cryptovillage/badge2017/assets/images/bender.png

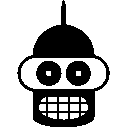
assets/images/bender.png
