cryptovillage/badge2017/assets/images/clubmate.png

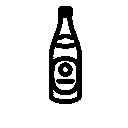
assets/images/clubmate.png
