cryptovillage/badge2017/assets/images/rot.png

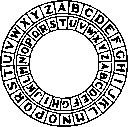
assets/images/rot.png
