cryptovillage/badge2017/assets/images/unlock.png

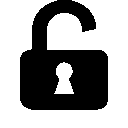
assets/images/unlock.png
