cryptovillage/badge2017/firmware/efm8ub1/src/InitDevice.c

//=========================================================
// src/InitDevice.c: generated by Hardware Configurator
//
// This file will be regenerated when saving a document.
// leave the sections inside the "$[...]" comment tags alone
// or they will be overwritten!
//=========================================================

// USER INCLUDES
#include <SI_EFM8UB1_Register_Enums.h>
#include "InitDevice.h"
#include "board.h"

// USER PROTOTYPES
// USER FUNCTIONS

// $[Library Includes]
#include "efm8_usb.h"
#include "descriptors.h"
#include "usb_0.h"
// [Library Includes]$

//==============================================================================
// enter_DefaultMode_from_RESET
//==============================================================================
extern void enter_DefaultMode_from_RESET(void) {
	// $[Config Calls]
	// Save the SFRPAGE
	uint8_t SFRPAGE_save = SFRPAGE;
	WDT_0_enter_DefaultMode_from_RESET();
	VREG_0_enter_DefaultMode_from_RESET();
	PORTS_0_enter_DefaultMode_from_RESET();
	PORTS_1_enter_DefaultMode_from_RESET();
	PORTS_2_enter_DefaultMode_from_RESET();
	PBCFG_0_enter_DefaultMode_from_RESET();
	ADC_0_enter_DefaultMode_from_RESET();
	CMP_0_enter_DefaultMode_from_RESET();
	CIP51_0_enter_DefaultMode_from_RESET();
	CLOCK_0_enter_DefaultMode_from_RESET();
	TIMER01_0_enter_DefaultMode_from_RESET();
	TIMER16_2_enter_DefaultMode_from_RESET();
	TIMER_SETUP_0_enter_DefaultMode_from_RESET();
	PCA_0_enter_DefaultMode_from_RESET();
	PCACH_0_enter_DefaultMode_from_RESET();
	SMBUS_0_enter_DefaultMode_from_RESET();
	SPI_0_enter_DefaultMode_from_RESET();
	UART_0_enter_DefaultMode_from_RESET();
	INTERRUPT_0_enter_DefaultMode_from_RESET();
	USBLIB_0_enter_DefaultMode_from_RESET();
	// Restore the SFRPAGE
	SFRPAGE = SFRPAGE_save;
	// [Config Calls]$
}

extern void VREG_0_enter_DefaultMode_from_RESET(void) {
	// $[REG0CN - Voltage Regulator 0 Control]
	// [REG0CN - Voltage Regulator 0 Control]$

	// $[REG1CN - Voltage Regulator 1 Control]
	/***********************************************************************
	 - Regulator is disabled
	 - Regulator bias is enabled
	 - The 5V regulator is in normal power mode
	 ***********************************************************************/
	SFRPAGE = 0x20;
	REG1CN = REG1CN_REG1ENB__DISABLED | REG1CN_BIASENB__ENABLED
			| REG1CN_SUSEN__NORMAL;
	// [REG1CN - Voltage Regulator 1 Control]$

}

extern void CIP51_0_enter_DefaultMode_from_RESET(void) {

	// $[PFE0CN - Prefetch Engine Control]
	/***********************************************************************
	 - Enable the prefetch engine 
	 - SYSCLK < 50 MHz
	 ***********************************************************************/
	SFRPAGE = 0x10;
	PFE0CN = PFE0CN_PFEN__ENABLED | PFE0CN_FLRT__SYSCLK_BELOW_50_MHZ;
	// [PFE0CN - Prefetch Engine Control]$

}

extern void PORTS_0_enter_DefaultMode_from_RESET(void) {
	// $[P0 - Port 0 Pin Latch]
	// [P0 - Port 0 Pin Latch]$

	// $[P0MDOUT - Port 0 Output Mode]
	/***********************************************************************
	 - P0.0 output is open-drain
	 - P0.1 output is open-drain
	 - P0.2 output is open-drain
	 - P0.3 output is open-drain
	 - P0.4 output is push-pull
	 - P0.5 output is open-drain
	 - P0.6 output is open-drain
	 - P0.7 output is open-drain
	 ***********************************************************************/
	SFRPAGE = 0x00;
	P0MDOUT = P0MDOUT_B0__OPEN_DRAIN | P0MDOUT_B1__OPEN_DRAIN
			| P0MDOUT_B2__OPEN_DRAIN | P0MDOUT_B3__OPEN_DRAIN
			| P0MDOUT_B4__PUSH_PULL | P0MDOUT_B5__OPEN_DRAIN
			| P0MDOUT_B6__OPEN_DRAIN | P0MDOUT_B7__OPEN_DRAIN;
	// [P0MDOUT - Port 0 Output Mode]$

	// $[P0MDIN - Port 0 Input Mode]
	/***********************************************************************
	 - P0.0 pin is configured for digital mode
	 - P0.1 pin is configured for digital mode
	 - P0.2 pin is configured for digital mode
	 - P0.3 pin is configured for digital mode
	 - P0.4 pin is configured for digital mode
	 - P0.5 pin is configured for digital mode
	 - P0.6 pin is configured for analog mode
	 - P0.7 pin is configured for analog mode
	 ***********************************************************************/
	P0MDIN = P0MDIN_B0__DIGITAL | P0MDIN_B1__DIGITAL | P0MDIN_B2__DIGITAL
			| P0MDIN_B3__DIGITAL | P0MDIN_B4__DIGITAL | P0MDIN_B5__DIGITAL
			| P0MDIN_B6__ANALOG | P0MDIN_B7__ANALOG;
	// [P0MDIN - Port 0 Input Mode]$

	// $[P0SKIP - Port 0 Skip]
	/***********************************************************************
	 - P0.0 pin is skipped by the crossbar
	 - P0.1 pin is skipped by the crossbar
	 - P0.2 pin is skipped by the crossbar
	 - P0.3 pin is skipped by the crossbar
	 - P0.4 pin is not skipped by the crossbar
	 - P0.5 pin is not skipped by the crossbar
	 - P0.6 pin is skipped by the crossbar
	 - P0.7 pin is skipped by the crossbar
	 ***********************************************************************/
	P0SKIP = P0SKIP_B0__SKIPPED | P0SKIP_B1__SKIPPED | P0SKIP_B2__SKIPPED
			| P0SKIP_B3__SKIPPED | P0SKIP_B4__NOT_SKIPPED
			| P0SKIP_B5__NOT_SKIPPED | P0SKIP_B6__SKIPPED | P0SKIP_B7__SKIPPED;
	// [P0SKIP - Port 0 Skip]$

	// $[P0MASK - Port 0 Mask]
	// [P0MASK - Port 0 Mask]$

	// $[P0MAT - Port 0 Match]
	// [P0MAT - Port 0 Match]$

	P0 = 0x0e;
}

extern void PBCFG_0_enter_DefaultMode_from_RESET(void) {
	// $[XBR2 - Port I/O Crossbar 2]
	/***********************************************************************
	 - Weak Pullups enabled 
	 - Crossbar enabled
	 - UART1 I/O unavailable at Port pin
	 - UART1 RTS1 unavailable at Port pin
	 - UART1 CTS1 unavailable at Port pin
	 ***********************************************************************/
	SFRPAGE = 0x00;
	XBR2 = XBR2_WEAKPUD__PULL_UPS_ENABLED | XBR2_XBARE__ENABLED
			| XBR2_URT1E__DISABLED | XBR2_URT1RTSE__DISABLED
			| XBR2_URT1CTSE__DISABLED;
	// [XBR2 - Port I/O Crossbar 2]$

	// $[PRTDRV - Port Drive Strength]
	// [PRTDRV - Port Drive Strength]$

	// $[XBR0 - Port I/O Crossbar 0]
	/***********************************************************************
	 - UART0 TX0, RX0 routed to Port pins P0.4 and P0.5
	 - SPI I/O routed to Port pins
	 - SMBus 0 I/O routed to Port pins
	 - CP0 unavailable at Port pin
	 - Asynchronous CP0 unavailable at Port pin
	 - CP1 unavailable at Port pin
	 - Asynchronous CP1 unavailable at Port pin
	 - SYSCLK unavailable at Port pin
	 ***********************************************************************/
	XBR0 = XBR0_URT0E__ENABLED | XBR0_SPI0E__ENABLED | XBR0_SMB0E__ENABLED
			| XBR0_CP0E__DISABLED | XBR0_CP0AE__DISABLED | XBR0_CP1E__DISABLED
			| XBR0_CP1AE__DISABLED | XBR0_SYSCKE__DISABLED;
	// [XBR0 - Port I/O Crossbar 0]$

	// $[XBR1 - Port I/O Crossbar 1]
	/***********************************************************************
	 - CEX0 routed to Port pin
	 - ECI unavailable at Port pin
	 - T0 unavailable at Port pin
	 - T1 unavailable at Port pin
	 - T2 unavailable at Port pin
	 ***********************************************************************/
	XBR1 = XBR1_PCA0ME__CEX0 | XBR1_ECIE__DISABLED | XBR1_T0E__DISABLED
			| XBR1_T1E__DISABLED | XBR1_T2E__DISABLED;
	// [XBR1 - Port I/O Crossbar 1]$

}

extern void CLOCK_0_enter_DefaultMode_from_RESET(void) {
	// $[HFOSC1 Setup]
	// Ensure SYSCLK is > 24 MHz before switching to HFOSC1
	SFRPAGE = 0x00;
	CLKSEL = CLKSEL_CLKSL__HFOSC0 | CLKSEL_CLKDIV__SYSCLK_DIV_1;
	while ((CLKSEL & CLKSEL_DIVRDY__BMASK) == CLKSEL_DIVRDY__NOT_READY)
		;
	// [HFOSC1 Setup]$

	// $[CLKSEL - Clock Select]
	/***********************************************************************
	 - Clock derived from the Internal High Frequency Oscillator 1
	 - SYSCLK is equal to selected clock source divided by 1
	 ***********************************************************************/
	CLKSEL = CLKSEL_CLKSL__HFOSC1 | CLKSEL_CLKDIV__SYSCLK_DIV_1;
	while ((CLKSEL & CLKSEL_DIVRDY__BMASK) == CLKSEL_DIVRDY__NOT_READY)
		;
	// [CLKSEL - Clock Select]$

}

extern void INTERRUPT_0_enter_DefaultMode_from_RESET(void) {
	// $[EIE1 - Extended Interrupt Enable 1]
	/***********************************************************************
	 - Enable interrupt requests generated by the ADINT flag
	 - Disable ADC0 Window Comparison interrupt
	 - Enable interrupt requests generated by the comparator 0 CPRIF or CPFIF
	 flags
	 - Disable CP1 interrupts
	 - Disable all Port Match interrupts
	 - Disable all PCA0 interrupts
	 - Enable interrupt requests generated by SMB0
	 - Disable Timer 3 interrupts
	 ***********************************************************************/
	EIE1 = EIE1_EADC0__ENABLED | EIE1_EWADC0__DISABLED | EIE1_ECP0__ENABLED
			| EIE1_ECP1__DISABLED | EIE1_EMAT__DISABLED | EIE1_EPCA0__DISABLED
			| EIE1_ESMB0__ENABLED | EIE1_ET3__DISABLED;
	// [EIE1 - Extended Interrupt Enable 1]$

	// $[EIE2 - Extended Interrupt Enable 2]
	/***********************************************************************
	 - Disable all I2C0 slave interrupts
	 - Disable Timer 4 interrupts
	 - Disable UART1 interrupts
	 - Disable all USB0 interrupts
	 - Enable interrupt requests generated by VBUS and VBUS and USB Charger
	 Detect
	 ***********************************************************************/
	SFRPAGE = 0x10;
	EIE2 = EIE2_EI2C0__DISABLED | EIE2_ET4__DISABLED | EIE2_ES1__DISABLED
			| EIE2_EUSB0__DISABLED | EIE2_EVBUS__ENABLED;
	// [EIE2 - Extended Interrupt Enable 2]$

	// $[EIP1H - Extended Interrupt Priority 1 High]
	// [EIP1H - Extended Interrupt Priority 1 High]$

	// $[EIP1 - Extended Interrupt Priority 1 Low]
	// [EIP1 - Extended Interrupt Priority 1 Low]$

	// $[EIP2 - Extended Interrupt Priority 2]
	// [EIP2 - Extended Interrupt Priority 2]$

	// $[EIP2H - Extended Interrupt Priority 2 High]
	// [EIP2H - Extended Interrupt Priority 2 High]$

	// $[IE - Interrupt Enable]
	/***********************************************************************
	 - Enable each interrupt according to its individual mask setting
	 - Disable external interrupt 0
	 - Disable external interrupt 1
	 - Enable interrupt requests generated by SPI0
	 - Disable all Timer 0 interrupt
	 - Disable all Timer 1 interrupt
	 - Enable interrupt requests generated by the TF2L or TF2H flags
	 - Enable UART0 interrupt
	 ***********************************************************************/
	SFRPAGE = 0x00;
	IE = IE_EA__ENABLED | IE_EX0__DISABLED | IE_EX1__DISABLED
			| IE_ESPI0__ENABLED | IE_ET0__DISABLED | IE_ET1__DISABLED
			| IE_ET2__ENABLED | IE_ES0__ENABLED;
	// [IE - Interrupt Enable]$

	// $[IP - Interrupt Priority]
	// [IP - Interrupt Priority]$

	// $[IPH - Interrupt Priority High]
	// [IPH - Interrupt Priority High]$

}

static const uint8_t code uuid[16] _at_ 0xFFC0;

extern void USBLIB_0_enter_DefaultMode_from_RESET(void) {
	// Read in UUID
	SI_SEGMENT_VARIABLE(hex[], static const uint8_t, SI_SEG_CODE) =
	{	'0', '1', '2', '3', '4', '5', '6', '7',
		'8', '9', 'a', 'b', 'c', 'd', 'e', 'f'};
	uint8_t i;

	for (i = 0; i < 16; i++) {
		serDesc[i * 2 + 3] = hex[(uuid[i] >> 4)];
		serDesc[i * 2 + 4] = hex[uuid[i] & 0xf];
	}

	// $[USBD Init]
	USBD_Init (&initstruct);
	// [USBD Init]$

}

extern void PORTS_1_enter_DefaultMode_from_RESET(void) {
	// $[P1 - Port 1 Pin Latch]
	// [P1 - Port 1 Pin Latch]$

	// $[P1MDOUT - Port 1 Output Mode]
	/***********************************************************************
	 - P1.0 output is push-pull
	 - P1.1 output is open-drain
	 - P1.2 output is push-pull
	 - P1.3 output is push-pull
	 - P1.4 output is open-drain
	 - P1.5 output is open-drain
	 - P1.6 output is open-drain
	 - P1.7 output is push-pull
	 ***********************************************************************/
	P1MDOUT = P1MDOUT_B0__PUSH_PULL | P1MDOUT_B1__OPEN_DRAIN
			| P1MDOUT_B2__PUSH_PULL | P1MDOUT_B3__PUSH_PULL
			| P1MDOUT_B4__OPEN_DRAIN | P1MDOUT_B5__OPEN_DRAIN
			| P1MDOUT_B6__OPEN_DRAIN | P1MDOUT_B7__PUSH_PULL;
	// [P1MDOUT - Port 1 Output Mode]$

	// $[P1MDIN - Port 1 Input Mode]
	// [P1MDIN - Port 1 Input Mode]$

	// $[P1SKIP - Port 1 Skip]
	/***********************************************************************
	 - P1.0 pin is not skipped by the crossbar
	 - P1.1 pin is not skipped by the crossbar
	 - P1.2 pin is not skipped by the crossbar
	 - P1.3 pin is skipped by the crossbar
	 - P1.4 pin is skipped by the crossbar
	 - P1.5 pin is not skipped by the crossbar
	 - P1.6 pin is not skipped by the crossbar
	 - P1.7 pin is skipped by the crossbar
	 ***********************************************************************/
	P1SKIP = P1SKIP_B0__NOT_SKIPPED | P1SKIP_B1__NOT_SKIPPED
			| P1SKIP_B2__NOT_SKIPPED | P1SKIP_B3__SKIPPED | P1SKIP_B4__SKIPPED
			| P1SKIP_B5__NOT_SKIPPED | P1SKIP_B6__NOT_SKIPPED
			| P1SKIP_B7__SKIPPED;
	// [P1SKIP - Port 1 Skip]$

	// $[P1MASK - Port 1 Mask]
	// [P1MASK - Port 1 Mask]$

	// $[P1MAT - Port 1 Match]
	// [P1MAT - Port 1 Match]$

	ESP32_EN = 0; // Disable ESP32 for now
	ESP32_BOOT = ESP32_BOOT_IDLE; // Don't enable BOOT pulldown
}

extern void SPI_0_enter_DefaultMode_from_RESET(void) {
	// $[SPI0CKR - SPI0 Clock Rate]
	/***********************************************************************
	 - SPI0 Clock Rate = 0x01
	 ***********************************************************************/
	SPI0CKR = (0x01 << SPI0CKR_SPI0CKR__SHIFT);
	// [SPI0CKR - SPI0 Clock Rate]$

	// $[SPI0FCN0 - SPI0 FIFO Control 0]
	/***********************************************************************
	 - RFRQ will be set anytime new data arrives in the RX FIFO 
	 - TFRQ will be set when the TX FIFO contains three or fewer bytes
	 - SPI0 interrupts will not be generated when RFRQ is set
	 - SPI0 interrupts will not be generated when TFRQ is set
	 ***********************************************************************/
	SFRPAGE = 0x20;
	SPI0FCN0 = SPI0FCN0_RXTH__ZERO | SPI0FCN0_TXTH__THREE
			| SPI0FCN0_RFRQE__DISABLED | SPI0FCN0_TFRQE__DISABLED;
	// [SPI0FCN0 - SPI0 FIFO Control 0]$

	// $[SPI0FCN1 - SPI0 FIFO Control 1]
	/***********************************************************************
	 - Received bytes will be discarded
	 - SPI0 interrupts will not be generated when SPIF is set
	 ***********************************************************************/
	SPI0FCN1 &= ~(SPI0FCN1_RXFIFOE__BMASK | SPI0FCN1_SPIFEN__BMASK);
	// [SPI0FCN1 - SPI0 FIFO Control 1]$

	// $[SPI0CFG - SPI0 Configuration]
	/***********************************************************************
	 - Enable master mode. Operate as a master
	 ***********************************************************************/
	SFRPAGE = 0x00;
	SPI0CFG |= SPI0CFG_MSTEN__MASTER_ENABLED;
	// [SPI0CFG - SPI0 Configuration]$

	// $[SPI0CN0 - SPI0 Control]
	/***********************************************************************
	 - Enable the SPI module
	 - 3-Wire Slave or 3-Wire Master Mode
	 ***********************************************************************/
	SPI0CN0 &= ~SPI0CN0_NSSMD__FMASK;
	SPI0CN0 |= SPI0CN0_SPIEN__ENABLED;
	// [SPI0CN0 - SPI0 Control]$

}

extern void PORTS_2_enter_DefaultMode_from_RESET(void) {
	// $[P2 - Port 2 Pin Latch]
	// [P2 - Port 2 Pin Latch]$

	// $[P2MDOUT - Port 2 Output Mode]
	/***********************************************************************
	 - P2.0 output is push-pull
	 - P2.1 output is push-pull
	 - P2.2 output is push-pull
	 - P2.3 output is push-pull
	 ***********************************************************************/
	P2MDOUT = P2MDOUT_B0__PUSH_PULL | P2MDOUT_B1__PUSH_PULL
			| P2MDOUT_B2__PUSH_PULL | P2MDOUT_B3__PUSH_PULL;
	// [P2MDOUT - Port 2 Output Mode]$

	// $[P2MDIN - Port 2 Input Mode]
	// [P2MDIN - Port 2 Input Mode]$

	// $[P2SKIP - Port 2 Skip]
	/***********************************************************************
	 - P2.0 pin is skipped by the crossbar
	 - P2.1 pin is not skipped by the crossbar
	 - P2.2 pin is not skipped by the crossbar
	 - P2.3 pin is not skipped by the crossbar
	 ***********************************************************************/
	SFRPAGE = 0x20;
	P2SKIP = P2SKIP_B0__SKIPPED | P2SKIP_B1__NOT_SKIPPED
			| P2SKIP_B2__NOT_SKIPPED | P2SKIP_B3__NOT_SKIPPED;
	// [P2SKIP - Port 2 Skip]$

	// $[P2MASK - Port 2 Mask]
	// [P2MASK - Port 2 Mask]$

	// $[P2MAT - Port 2 Match]
	// [P2MAT - Port 2 Match]$

	MIC_SHDN = 1; // Shut down MIC amp for now
	BC_EN_1 = 0; // Disable charging
	BC_EN_2 = 0; // Disable charging
}

extern void ADC_0_enter_DefaultMode_from_RESET(void) {
	// $[ADC0CN1 - ADC0 Control 1]
	// [ADC0CN1 - ADC0 Control 1]$

	// $[ADC0MX - ADC0 Multiplexer Selection]
	/***********************************************************************
	 - Select ADC0.7
	 ***********************************************************************/
	ADC0MX = ADC0MX_ADC0MX__ADC0P7;
	// [ADC0MX - ADC0 Multiplexer Selection]$

	// $[ADC0CF - ADC0 Configuration]
	/***********************************************************************
	 - SAR Clock Divider = 0x06
	 - ADC0 operates in 10-bit or 12-bit mode 
	 - The on-chip PGA gain is 1
	 - Normal Track Mode
	 ***********************************************************************/
	ADC0CF = (0x06 << ADC0CF_ADSC__SHIFT) | ADC0CF_AD8BE__NORMAL
			| ADC0CF_ADGN__GAIN_1 | ADC0CF_ADTM__TRACK_NORMAL;
	// [ADC0CF - ADC0 Configuration]$

	// $[ADC0AC - ADC0 Accumulator Configuration]
	// [ADC0AC - ADC0 Accumulator Configuration]$

	// $[ADC0TK - ADC0 Burst Mode Track Time]
	// [ADC0TK - ADC0 Burst Mode Track Time]$

	// $[ADC0PWR - ADC0 Power Control]
	/***********************************************************************
	 - Burst Mode Power Up Time = 0x0F
	 - Enable low power mode 
	 - Low power mode disabled
	 - Select bias current mode 1 
	 ***********************************************************************/
	ADC0PWR = (0x0F << ADC0PWR_ADPWR__SHIFT) | ADC0PWR_ADLPM__LP_BUFFER_ENABLED
			| ADC0PWR_ADMXLP__LP_MUX_VREF_DISABLED | ADC0PWR_ADBIAS__MODE1;
	// [ADC0PWR - ADC0 Power Control]$

	// $[ADC0GTH - ADC0 Greater-Than High Byte]
	// [ADC0GTH - ADC0 Greater-Than High Byte]$

	// $[ADC0GTL - ADC0 Greater-Than Low Byte]
	// [ADC0GTL - ADC0 Greater-Than Low Byte]$

	// $[ADC0LTH - ADC0 Less-Than High Byte]
	// [ADC0LTH - ADC0 Less-Than High Byte]$

	// $[ADC0LTL - ADC0 Less-Than Low Byte]
	// [ADC0LTL - ADC0 Less-Than Low Byte]$

	// $[ADC0CN0 - ADC0 Control 0]
	/***********************************************************************
	 - Enable ADC0 burst mode
	 ***********************************************************************/
	ADC0CN0 |= ADC0CN0_ADBMEN__BURST_ENABLED;
	// [ADC0CN0 - ADC0 Control 0]$

}

extern void TIMER_SETUP_0_enter_DefaultMode_from_RESET(void) {
	// $[CKCON0 - Clock Control 0]
	/***********************************************************************
	 - System clock divided by 12
	 - Counter/Timer 0 uses the system clock
	 - Timer 2 high byte uses the clock defined by T2XCLK in TMR2CN0
	 - Timer 2 low byte uses the clock defined by T2XCLK in TMR2CN0
	 - Timer 3 high byte uses the clock defined by T3XCLK in TMR3CN0
	 - Timer 3 low byte uses the clock defined by T3XCLK in TMR3CN0
	 - Timer 1 uses the system clock
	 ***********************************************************************/
	CKCON0 = CKCON0_SCA__SYSCLK_DIV_12 | CKCON0_T0M__SYSCLK
			| CKCON0_T2MH__EXTERNAL_CLOCK | CKCON0_T2ML__EXTERNAL_CLOCK
			| CKCON0_T3MH__EXTERNAL_CLOCK | CKCON0_T3ML__EXTERNAL_CLOCK
			| CKCON0_T1M__SYSCLK;
	// [CKCON0 - Clock Control 0]$

	// $[CKCON1 - Clock Control 1]
	// [CKCON1 - Clock Control 1]$

	// $[TMOD - Timer 0/1 Mode]
	/***********************************************************************
	 - Mode 2, 8-bit Counter/Timer with Auto-Reload
	 - Mode 2, 8-bit Counter/Timer with Auto-Reload
	 - Timer Mode
	 - Timer 0 enabled when TR0 = 1 irrespective of INT0 logic level
	 - Timer Mode
	 - Timer 1 enabled when TR1 = 1 irrespective of INT1 logic level
	 ***********************************************************************/
	TMOD = TMOD_T0M__MODE2 | TMOD_T1M__MODE2 | TMOD_CT0__TIMER
			| TMOD_GATE0__DISABLED | TMOD_CT1__TIMER | TMOD_GATE1__DISABLED;
	// [TMOD - Timer 0/1 Mode]$

	// $[TCON - Timer 0/1 Control]
	/***********************************************************************
	 - Start Timer 0 running
	 - Start Timer 1 running
	 ***********************************************************************/
	TCON |= TCON_TR0__RUN | TCON_TR1__RUN;
	// [TCON - Timer 0/1 Control]$

}

extern void UART_0_enter_DefaultMode_from_RESET(void) {
	// $[SCON0 - UART0 Serial Port Control]
	/***********************************************************************
	 - UART0 reception enabled
	 ***********************************************************************/
	SCON0 |= SCON0_REN__RECEIVE_ENABLED;
	// [SCON0 - UART0 Serial Port Control]$

}

extern void SMBUS_0_enter_DefaultMode_from_RESET(void) {
	// $[SMB0FCN0 - SMBus0 FIFO Control 0]
	// [SMB0FCN0 - SMBus0 FIFO Control 0]$

	// $[SMB0RXLN - SMBus0 Receive Length Counter]
	// [SMB0RXLN - SMBus0 Receive Length Counter]$

	// $[SMB0ADR - SMBus 0 Slave Address]
	/***********************************************************************
	 - General Call Address is ignored
	 - SMBus Hardware Slave Address = 0x64
	 ***********************************************************************/
	SMB0ADR = SMB0ADR_GC__IGNORED | (0x64 << SMB0ADR_SLV__SHIFT);
	// [SMB0ADR - SMBus 0 Slave Address]$

	// $[SMB0ADM - SMBus 0 Slave Address Mask]
	/***********************************************************************
	 - Automatic slave address recognition and hardware acknowledge is
	 enabled
	 - SMBus Slave Address Mask = 0x7F
	 ***********************************************************************/
	SMB0ADM = SMB0ADM_EHACK__ADR_ACK_AUTOMATIC | (0x7F << SMB0ADM_SLVM__SHIFT);
	// [SMB0ADM - SMBus 0 Slave Address Mask]$

	// $[SMB0TC - SMBus 0 Timing and Pin Control]
	// [SMB0TC - SMBus 0 Timing and Pin Control]$

	// $[SMB0CF - SMBus 0 Configuration]
	/***********************************************************************
	 - Slave states are inhibited
	 - Enable the SMBus module
	 ***********************************************************************/
	SMB0CF |= SMB0CF_INH__SLAVE_DISABLED | SMB0CF_ENSMB__ENABLED;
	// [SMB0CF - SMBus 0 Configuration]$

}

extern void TIMER01_0_enter_DefaultMode_from_RESET(void) {
	// $[Timer Initialization]
	//Save Timer Configuration
	uint8_t TCON_save;
	TCON_save = TCON;
	//Stop Timers
	TCON &= ~TCON_TR0__BMASK & ~TCON_TR1__BMASK;

	// [Timer Initialization]$

	// $[TH0 - Timer 0 High Byte]
	/***********************************************************************
	 - Timer 0 High Byte = 0xD8
	 ***********************************************************************/
	TH0 = (0xD8 << TH0_TH0__SHIFT);
	// [TH0 - Timer 0 High Byte]$

	// $[TL0 - Timer 0 Low Byte]
	// [TL0 - Timer 0 Low Byte]$

	// $[TH1 - Timer 1 High Byte]
	/***********************************************************************
	 - Timer 1 High Byte = 0x30
	 ***********************************************************************/
	TH1 = (0x30 << TH1_TH1__SHIFT);
	// [TH1 - Timer 1 High Byte]$

	// $[TL1 - Timer 1 Low Byte]
	// [TL1 - Timer 1 Low Byte]$

	// $[Timer Restoration]
	//Restore Timer Configuration
	TCON |= (TCON_save & TCON_TR0__BMASK) | (TCON_save & TCON_TR1__BMASK);

	// [Timer Restoration]$

}

extern void WDT_0_enter_DefaultMode_from_RESET(void) {
	// $[WDTCN - Watchdog Timer Control]
	SFRPAGE = 0x00;
	//Disable Watchdog with key sequence
	WDTCN = 0xDE; //First key
	WDTCN = 0xAD; //Second key
	// [WDTCN - Watchdog Timer Control]$
	// WDTCN = 0xff; // Prevent watchdog from being disabled
}

extern void CMP_0_enter_DefaultMode_from_RESET(void) {
	// $[CMP0MX - Comparator 0 Multiplexer Selection]
	/***********************************************************************
	 - External pin CMP0P.8
	 - External pin CMP0N.6
	 ***********************************************************************/
	uint8_t delay;

	CMP0MX = CMP0MX_CMXP__CMP0P8 | CMP0MX_CMXN__CMP0N6;
	// Delay to allow the comparator inputs to settle
	for (delay = 0; delay < 0x20; delay++)
		;
	// [CMP0MX - Comparator 0 Multiplexer Selection]$

	// $[CMP0CN1 - Comparator 0 Control 1]
	// [CMP0CN1 - Comparator 0 Control 1]$

	// $[CMP0MD - Comparator 0 Mode]
	/***********************************************************************
	 - Mode 3 
	 - Output is inverted
	 - Comparator falling-edge interrupt enabled
	 - Comparator rising-edge interrupt enabled
	 ***********************************************************************/
	CMP0MD |= CMP0MD_CPMD__MODE3 | CMP0MD_CPINV__INVERT
			| CMP0MD_CPFIE__FALL_INT_ENABLED | CMP0MD_CPRIE__RISE_INT_ENABLED;
	// [CMP0MD - Comparator 0 Mode]$

	// $[CMP0CN0 - Comparator 0 Control 0]
	/***********************************************************************
	 - Comparator enabled
	 - Positive Hysteresis = Hysteresis 3 
	 - Negative Hysteresis = Hysteresis 3 
	 ***********************************************************************/
	CMP0CN0 |= CMP0CN0_CPEN__ENABLED | CMP0CN0_CPHYP__ENABLED_MODE3
			| CMP0CN0_CPHYN__ENABLED_MODE3;
	// [CMP0CN0 - Comparator 0 Control 0]$

}

extern void PCA_0_enter_DefaultMode_from_RESET(void) {
	// $[PCA Off]
	PCA0CN0_CR = PCA0CN0_CR__STOP;
	// [PCA Off]$

	// $[PCA0MD - PCA Mode]
	// [PCA0MD - PCA Mode]$

	// $[PCA0CENT - PCA Center Alignment Enable]
	// [PCA0CENT - PCA Center Alignment Enable]$

	// $[PCA0CLR - PCA Comparator Clear Control]
	// [PCA0CLR - PCA Comparator Clear Control]$

	// $[PCA0L - PCA Counter/Timer Low Byte]
	// [PCA0L - PCA Counter/Timer Low Byte]$

	// $[PCA0H - PCA Counter/Timer High Byte]
	// [PCA0H - PCA Counter/Timer High Byte]$

	// $[PCA0POL - PCA Output Polarity]
	/***********************************************************************
	 - Invert polarity
	 - Use default polarity
	 - Use default polarity
	 ***********************************************************************/
	PCA0POL = PCA0POL_CEX0POL__INVERT | PCA0POL_CEX1POL__DEFAULT
			| PCA0POL_CEX2POL__DEFAULT;
	// [PCA0POL - PCA Output Polarity]$

	// $[PCA0PWM - PCA PWM Configuration]
	// [PCA0PWM - PCA PWM Configuration]$

	// $[PCA On]
	PCA0CN0_CR = PCA0CN0_CR__RUN;
	// [PCA On]$

}

extern void PCACH_0_enter_DefaultMode_from_RESET(void) {
	// $[PCA0 Settings Save]
	// Select Capture/Compare register)
	PCA0PWM &= ~PCA0PWM_ARSEL__BMASK;
	// [PCA0 Settings Save]$

	// $[PCA0CPM0 - PCA Channel 0 Capture/Compare Mode]
	/***********************************************************************
	 - Disable negative edge capture
	 - Disable CCF0 interrupts
	 - Disable match function
	 - 8 to 11-bit PWM selected
	 - Disable positive edge capture
	 - Enable comparator function
	 - Enable PWM function
	 - Disable toggle function
	 ***********************************************************************/
	PCA0CPM0 = PCA0CPM0_CAPN__DISABLED | PCA0CPM0_ECCF__DISABLED
			| PCA0CPM0_MAT__DISABLED | PCA0CPM0_PWM16__8_BIT
			| PCA0CPM0_CAPP__DISABLED | PCA0CPM0_ECOM__ENABLED
			| PCA0CPM0_PWM__ENABLED | PCA0CPM0_TOG__DISABLED;
	// [PCA0CPM0 - PCA Channel 0 Capture/Compare Mode]$

	// $[PCA0CPL0 - PCA Channel 0 Capture Module Low Byte]
	// [PCA0CPL0 - PCA Channel 0 Capture Module Low Byte]$

	// $[PCA0CPH0 - PCA Channel 0 Capture Module High Byte]
	// [PCA0CPH0 - PCA Channel 0 Capture Module High Byte]$

	// $[Auto-reload]
	// [Auto-reload]$

	// $[PCA0 Settings Restore]
	// [PCA0 Settings Restore]$

}

extern void TIMER16_2_enter_DefaultMode_from_RESET(void) {
	// $[Timer Initialization]
	// Save Timer Configuration
	uint8_t TMR2CN0_TR2_save;
	TMR2CN0_TR2_save = TMR2CN0 & TMR2CN0_TR2__BMASK;
	// Stop Timer
	TMR2CN0 &= ~(TMR2CN0_TR2__BMASK);
	// [Timer Initialization]$

	// $[TMR2CN1 - Timer 2 Control 1]
	// [TMR2CN1 - Timer 2 Control 1]$

	// $[TMR2CN0 - Timer 2 Control]
	// [TMR2CN0 - Timer 2 Control]$

	// $[TMR2H - Timer 2 High Byte]
	// [TMR2H - Timer 2 High Byte]$

	// $[TMR2L - Timer 2 Low Byte]
	// [TMR2L - Timer 2 Low Byte]$

	// $[TMR2RLH - Timer 2 Reload High Byte]
	/***********************************************************************
	 - Timer 2 Reload High Byte = 0xFE
	 ***********************************************************************/
	TMR2RLH = (0xFE << TMR2RLH_TMR2RLH__SHIFT);
	// [TMR2RLH - Timer 2 Reload High Byte]$

	// $[TMR2RLL - Timer 2 Reload Low Byte]
	/***********************************************************************
	 - Timer 2 Reload Low Byte = 0x70
	 ***********************************************************************/
	TMR2RLL = (0x70 << TMR2RLL_TMR2RLL__SHIFT);
	// [TMR2RLL - Timer 2 Reload Low Byte]$

	// $[TMR2CN0]
	/***********************************************************************
	 - Start Timer 2 running
	 ***********************************************************************/
	TMR2CN0 |= TMR2CN0_TR2__RUN;
	// [TMR2CN0]$

	// $[Timer Restoration]
	// Restore Timer Configuration
	TMR2CN0 |= TMR2CN0_TR2_save;
	// [Timer Restoration]$

}
