cryptovillage/badge2017/firmware/esp32/components/micropython/src/modmachine.c

/*
 * This file is part of the MicroPython project, http://micropython.org/
 *
 * Development of the code in this file was sponsored by Microbric Pty Ltd
 *
 * The MIT License (MIT)
 *
 * Copyright (c) 2013-2015 Damien P. George
 * Copyright (c) 2016 Paul Sokolovsky
 *
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
 * THE SOFTWARE IS PROVIDED "AS IS", WITHOUT WARRANTY OF ANY KIND, EXPRESS OR
 * IMPLIED, INCLUDING BUT NOT LIMITED TO THE WARRANTIES OF MERCHANTABILITY,
 * FITNESS FOR A PARTICULAR PURPOSE AND NONINFRINGEMENT. IN NO EVENT SHALL THE
 * AUTHORS OR COPYRIGHT HOLDERS BE LIABLE FOR ANY CLAIM, DAMAGES OR OTHER
 * LIABILITY, WHETHER IN AN ACTION OF CONTRACT, TORT OR OTHERWISE, ARISING FROM,
 * OUT OF OR IN CONNECTION WITH THE SOFTWARE OR THE USE OR OTHER DEALINGS IN
 * THE SOFTWARE.
 */

#include <stdint.h>
#include <stdio.h>

#include "freertos/FreeRTOS.h"
#include "freertos/task.h"
#include "rom/ets_sys.h"
#include "esp_system.h"

#include "py/obj.h"
#include "py/runtime.h"
#include "extmod/machine_mem.h"
#include "extmod/machine_pulse.h"
#include "extmod/machine_i2c.h"
#include "extmod/machine_spi.h"
#include "modmachine.h"

#if MICROPY_PY_MACHINE

STATIC mp_obj_t machine_freq(size_t n_args, const mp_obj_t *args) {
    if (n_args == 0) {
        // get
        return mp_obj_new_int(ets_get_cpu_frequency() * 1000000);
    } else {
        // set
        mp_int_t freq = mp_obj_get_int(args[0]) / 1000000;
        if (freq != 80 && freq != 160 && freq != 240) {
            nlr_raise(mp_obj_new_exception_msg(&mp_type_ValueError,
                "frequency can only be either 80Mhz, 160MHz or 240MHz"));
        }
        /*
        system_update_cpu_freq(freq);
        */
        return mp_const_none;
    }
}
STATIC MP_DEFINE_CONST_FUN_OBJ_VAR_BETWEEN(machine_freq_obj, 0, 1, machine_freq);

STATIC mp_obj_t machine_reset(void) {
    esp_restart();
    return mp_const_none;
}
STATIC MP_DEFINE_CONST_FUN_OBJ_0(machine_reset_obj, machine_reset);

STATIC mp_obj_t machine_unique_id(void) {
    uint8_t chipid[6];
    esp_efuse_mac_get_default(chipid);
    return mp_obj_new_bytes(chipid, 6);
}
STATIC MP_DEFINE_CONST_FUN_OBJ_0(machine_unique_id_obj, machine_unique_id);

STATIC mp_obj_t machine_idle(void) {
    taskYIELD();
    return mp_const_none;
}
STATIC MP_DEFINE_CONST_FUN_OBJ_0(machine_idle_obj, machine_idle);

STATIC mp_obj_t machine_disable_irq(void) {
    uint32_t state = MICROPY_BEGIN_ATOMIC_SECTION();
    return mp_obj_new_int(state);
}
MP_DEFINE_CONST_FUN_OBJ_0(machine_disable_irq_obj, machine_disable_irq);

STATIC mp_obj_t machine_enable_irq(mp_obj_t state_in) {
    uint32_t state = mp_obj_get_int(state_in);
    MICROPY_END_ATOMIC_SECTION(state);
    return mp_const_none;
}
MP_DEFINE_CONST_FUN_OBJ_1(machine_enable_irq_obj, machine_enable_irq);

STATIC const mp_rom_map_elem_t machine_module_globals_table[] = {
    { MP_ROM_QSTR(MP_QSTR___name__), MP_ROM_QSTR(MP_QSTR_umachine) },

	/*
    { MP_ROM_QSTR(MP_QSTR_mem8), MP_ROM_PTR(&machine_mem8_obj) },
    { MP_ROM_QSTR(MP_QSTR_mem16), MP_ROM_PTR(&machine_mem16_obj) },
    { MP_ROM_QSTR(MP_QSTR_mem32), MP_ROM_PTR(&machine_mem32_obj) },
    */

    { MP_ROM_QSTR(MP_QSTR_freq), MP_ROM_PTR(&machine_freq_obj) },
    { MP_ROM_QSTR(MP_QSTR_reset), MP_ROM_PTR(&machine_reset_obj) },
    { MP_ROM_QSTR(MP_QSTR_unique_id), MP_ROM_PTR(&machine_unique_id_obj) },
    { MP_ROM_QSTR(MP_QSTR_idle), MP_ROM_PTR(&machine_idle_obj) },

	/*
    { MP_ROM_QSTR(MP_QSTR_disable_irq), MP_ROM_PTR(&machine_disable_irq_obj) },
    { MP_ROM_QSTR(MP_QSTR_enable_irq), MP_ROM_PTR(&machine_enable_irq_obj) },

    { MP_ROM_QSTR(MP_QSTR_time_pulse_us), MP_ROM_PTR(&machine_time_pulse_us_obj) },
    */

	/*
    { MP_ROM_QSTR(MP_QSTR_Timer), MP_ROM_PTR(&machine_timer_type) },
    { MP_ROM_QSTR(MP_QSTR_Pin), MP_ROM_PTR(&machine_pin_type) },
    { MP_ROM_QSTR(MP_QSTR_TouchPad), MP_ROM_PTR(&machine_touchpad_type) },
    { MP_ROM_QSTR(MP_QSTR_ADC), MP_ROM_PTR(&machine_adc_type) },
    { MP_ROM_QSTR(MP_QSTR_DAC), MP_ROM_PTR(&machine_dac_type) },
    { MP_ROM_QSTR(MP_QSTR_I2C), MP_ROM_PTR(&machine_i2c_type) },
    { MP_ROM_QSTR(MP_QSTR_PWM), MP_ROM_PTR(&machine_pwm_type) },
    { MP_ROM_QSTR(MP_QSTR_SPI), MP_ROM_PTR(&mp_machine_soft_spi_type) },
    { MP_ROM_QSTR(MP_QSTR_UART), MP_ROM_PTR(&machine_uart_type) },
    */
};

STATIC MP_DEFINE_CONST_DICT(machine_module_globals, machine_module_globals_table);

const mp_obj_module_t mp_module_machine = {
    .base = { &mp_type_module },
    .globals = (mp_obj_dict_t*)&machine_module_globals,
};

#endif // MICROPY_PY_MACHINE
