cryptovillage/badge2017/firmware/esp32/components/micropython/src/moduos.c

/*
 * This file is part of the MicroPython project, http://micropython.org/
 *
 * Development of the code in this file was sponsored by Microbric Pty Ltd
 *
 * The MIT License (MIT)
 *
 * Copyright (c) 2015 Josef Gajdusek
 * Copyright (c) 2016 Damien P. George
 *
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
 * THE SOFTWARE IS PROVIDED "AS IS", WITHOUT WARRANTY OF ANY KIND, EXPRESS OR
 * IMPLIED, INCLUDING BUT NOT LIMITED TO THE WARRANTIES OF MERCHANTABILITY,
 * FITNESS FOR A PARTICULAR PURPOSE AND NONINFRINGEMENT. IN NO EVENT SHALL THE
 * AUTHORS OR COPYRIGHT HOLDERS BE LIABLE FOR ANY CLAIM, DAMAGES OR OTHER
 * LIABILITY, WHETHER IN AN ACTION OF CONTRACT, TORT OR OTHERWISE, ARISING FROM,
 * OUT OF OR IN CONNECTION WITH THE SOFTWARE OR THE USE OR OTHER DEALINGS IN
 * THE SOFTWARE.
 */

#include <string.h>
#include <sys/types.h>
#include <sys/stat.h>
#include <dirent.h>
#include <unistd.h>
#include <errno.h>

#include "esp_system.h"

#include "py/mpconfig.h"
#include "py/obj.h"
#include "py/objstr.h"
#include "py/runtime.h"
#include "py/mperrno.h"
#include "genhdr/mpversion.h"
#include "extmod/misc.h"

#include "mphalport.h"

STATIC const qstr os_uname_info_fields[] = {
    MP_QSTR_sysname, MP_QSTR_nodename,
    MP_QSTR_release, MP_QSTR_version, MP_QSTR_machine
};
STATIC const MP_DEFINE_STR_OBJ(os_uname_info_sysname_obj, MICROPY_PY_SYS_PLATFORM);
STATIC const MP_DEFINE_STR_OBJ(os_uname_info_nodename_obj, MICROPY_PY_SYS_PLATFORM);
STATIC const MP_DEFINE_STR_OBJ(os_uname_info_release_obj, MICROPY_VERSION_STRING);
STATIC const MP_DEFINE_STR_OBJ(os_uname_info_version_obj, MICROPY_GIT_TAG " on " MICROPY_BUILD_DATE);
STATIC const MP_DEFINE_STR_OBJ(os_uname_info_machine_obj, MICROPY_HW_BOARD_NAME " with " MICROPY_HW_MCU_NAME);

STATIC MP_DEFINE_ATTRTUPLE(
    os_uname_info_obj,
    os_uname_info_fields,
    5,
    (mp_obj_t)&os_uname_info_sysname_obj,
    (mp_obj_t)&os_uname_info_nodename_obj,
    (mp_obj_t)&os_uname_info_release_obj,
    (mp_obj_t)&os_uname_info_version_obj,
    (mp_obj_t)&os_uname_info_machine_obj
);

STATIC mp_obj_t mod_os_unlink(mp_obj_t path_in) {
    const char *path = mp_obj_str_get_str(path_in);

    int r = unlink(path);

    RAISE_ERRNO(r, errno);

    return mp_const_none;
}
STATIC MP_DEFINE_CONST_FUN_OBJ_1(mod_os_unlink_obj, mod_os_unlink);

STATIC mp_obj_t mod_os_stat(mp_obj_t path_in) {
    struct stat sb;
    const char *path = mp_obj_str_get_str(path_in);

    int res = stat(path, &sb);
    RAISE_ERRNO(res, errno);

    mp_obj_tuple_t *t = MP_OBJ_TO_PTR(mp_obj_new_tuple(10, NULL));
    t->items[0] = MP_OBJ_NEW_SMALL_INT(sb.st_mode);
    t->items[1] = MP_OBJ_NEW_SMALL_INT(sb.st_ino);
    t->items[2] = MP_OBJ_NEW_SMALL_INT(sb.st_dev);
    t->items[3] = MP_OBJ_NEW_SMALL_INT(sb.st_nlink);
    t->items[4] = MP_OBJ_NEW_SMALL_INT(sb.st_uid);
    t->items[5] = MP_OBJ_NEW_SMALL_INT(sb.st_gid);
    t->items[6] = MP_OBJ_NEW_SMALL_INT(sb.st_size);
    t->items[7] = MP_OBJ_NEW_SMALL_INT(sb.st_atime);
    t->items[8] = MP_OBJ_NEW_SMALL_INT(sb.st_mtime);
    t->items[9] = MP_OBJ_NEW_SMALL_INT(sb.st_ctime);
    return MP_OBJ_FROM_PTR(t);
}
STATIC MP_DEFINE_CONST_FUN_OBJ_1(mod_os_stat_obj, mod_os_stat);

STATIC mp_obj_t mod_os_mkdir(mp_obj_t path_in) {
    // TODO: Accept mode param
    const char *path = mp_obj_str_get_str(path_in);
    int r = mkdir(path, 0777);
    RAISE_ERRNO(r, errno);
    return mp_const_none;
}
STATIC MP_DEFINE_CONST_FUN_OBJ_1(mod_os_mkdir_obj, mod_os_mkdir);

typedef struct _mp_obj_listdir_t {
    mp_obj_base_t base;
    mp_fun_1_t iternext;
    DIR *dir;
} mp_obj_listdir_t;

STATIC mp_obj_t listdir_next(mp_obj_t self_in) {
    mp_obj_listdir_t *self = MP_OBJ_TO_PTR(self_in);

    if (self->dir == NULL) {
        goto done;
    }
    struct dirent *dirent = readdir(self->dir);
    if (dirent == NULL) {
        closedir(self->dir);
        self->dir = NULL;
    done:
        return MP_OBJ_STOP_ITERATION;
    }

    mp_obj_tuple_t *t = MP_OBJ_TO_PTR(mp_obj_new_tuple(3, NULL));
    t->items[0] = mp_obj_new_str(dirent->d_name, strlen(dirent->d_name));
    #ifdef _DIRENT_HAVE_D_TYPE
    t->items[1] = MP_OBJ_NEW_SMALL_INT(dirent->d_type);
    #else
    // DT_UNKNOWN should have 0 value on any reasonable system
    t->items[1] = MP_OBJ_NEW_SMALL_INT(0);
    #endif
    #ifdef _DIRENT_HAVE_D_INO
    t->items[2] = MP_OBJ_NEW_SMALL_INT(dirent->d_ino);
    #else
    t->items[2] = MP_OBJ_NEW_SMALL_INT(0);
    #endif
    return MP_OBJ_FROM_PTR(t);
}

STATIC mp_obj_t mod_os_ilistdir(size_t n_args, const mp_obj_t *args) {
    const char *path = ".";
    if (n_args > 0) {
        path = mp_obj_str_get_str(args[0]);
    }
    mp_obj_listdir_t *o = m_new_obj(mp_obj_listdir_t);
    o->base.type = &mp_type_polymorph_iter;
    o->dir = opendir(path);
    o->iternext = listdir_next;
    return MP_OBJ_FROM_PTR(o);
}
STATIC MP_DEFINE_CONST_FUN_OBJ_VAR_BETWEEN(mod_os_ilistdir_obj, 0, 1, mod_os_ilistdir);

STATIC mp_obj_t mod_os_errno(size_t n_args, const mp_obj_t *args) {
    if (n_args == 0) {
        return MP_OBJ_NEW_SMALL_INT(errno);
    }

    errno = mp_obj_get_int(args[0]);
    return mp_const_none;
}
STATIC MP_DEFINE_CONST_FUN_OBJ_VAR_BETWEEN(mod_os_errno_obj, 0, 1, mod_os_errno);

STATIC mp_obj_t os_uname(void) {
    return (mp_obj_t)&os_uname_info_obj;
}
STATIC MP_DEFINE_CONST_FUN_OBJ_0(os_uname_obj, os_uname);

STATIC mp_obj_t os_urandom(mp_obj_t num) {
    mp_int_t n = mp_obj_get_int(num);
    vstr_t vstr;
    vstr_init_len(&vstr, n);
    uint32_t r = 0;
    for (int i = 0; i < n; i++) {
        if ((i & 3) == 0) {
            r = esp_random(); // returns 32-bit hardware random number
        }
        vstr.buf[i] = r;
        r >>= 8;
    }
    return mp_obj_new_str_from_vstr(&mp_type_bytes, &vstr);
}
STATIC MP_DEFINE_CONST_FUN_OBJ_1(os_urandom_obj, os_urandom);

#if MICROPY_PY_OS_DUPTERM
STATIC mp_obj_t os_dupterm_notify(mp_obj_t obj_in) {
    (void)obj_in;
    //mp_hal_signal_dupterm_input();
    return mp_const_none;
}
STATIC MP_DEFINE_CONST_FUN_OBJ_1(os_dupterm_notify_obj, os_dupterm_notify);
#endif

STATIC const mp_rom_map_elem_t os_module_globals_table[] = {
    { MP_ROM_QSTR(MP_QSTR___name__), MP_ROM_QSTR(MP_QSTR_uos) },
    { MP_ROM_QSTR(MP_QSTR_uname), MP_ROM_PTR(&os_uname_obj) },
    { MP_ROM_QSTR(MP_QSTR_urandom), MP_ROM_PTR(&os_urandom_obj) },
    #if MICROPY_PY_OS_DUPTERM
    { MP_ROM_QSTR(MP_QSTR_dupterm), MP_ROM_PTR(&mp_uos_dupterm_obj) },
    { MP_ROM_QSTR(MP_QSTR_dupterm_notify), MP_ROM_PTR(&os_dupterm_notify_obj) },
    #endif
    { MP_ROM_QSTR(MP_QSTR_ilistdir), MP_ROM_PTR(&mod_os_ilistdir_obj) },
    { MP_ROM_QSTR(MP_QSTR_mkdir), MP_ROM_PTR(&mod_os_mkdir_obj) },
    { MP_ROM_QSTR(MP_QSTR_stat), MP_ROM_PTR(&mod_os_stat_obj) },
	{ MP_ROM_QSTR(MP_QSTR_unlink), MP_ROM_PTR(&mod_os_unlink_obj) },
};

STATIC MP_DEFINE_CONST_DICT(os_module_globals, os_module_globals_table);

const mp_obj_module_t uos_module = {
    .base = { &mp_type_module },
    .globals = (mp_obj_dict_t*)&os_module_globals,
};
