cryptovillage/badge2017/firmware/esp32/components/micropython/src/mp.c

/*
 * This file is part of the MicroPython project, http://micropython.org/
 *
 * Development of the code in this file was sponsored by Microbric Pty Ltd
 *
 * The MIT License (MIT)
 *
 * Copyright (c) 2016 Damien P. George
 *
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
 * THE SOFTWARE IS PROVIDED "AS IS", WITHOUT WARRANTY OF ANY KIND, EXPRESS OR
 * IMPLIED, INCLUDING BUT NOT LIMITED TO THE WARRANTIES OF MERCHANTABILITY,
 * FITNESS FOR A PARTICULAR PURPOSE AND NONINFRINGEMENT. IN NO EVENT SHALL THE
 * AUTHORS OR COPYRIGHT HOLDERS BE LIABLE FOR ANY CLAIM, DAMAGES OR OTHER
 * LIABILITY, WHETHER IN AN ACTION OF CONTRACT, TORT OR OTHERWISE, ARISING FROM,
 * OUT OF OR IN CONNECTION WITH THE SOFTWARE OR THE USE OR OTHER DEALINGS IN
 * THE SOFTWARE.
 */

#include "mpconfigport.h"

#include <stdio.h>
#include <string.h>
#include <sys/stat.h>

#include "freertos/FreeRTOS.h"
#include "freertos/task.h"
#include "esp_system.h"
#include "esp_heap_caps.h"
#include "esp_log.h"
#include "nvs_flash.h"
#include "esp_task.h"
#include "soc/cpu.h"

#include "driver/uart.h"

#include "py/stackctrl.h"
#include "py/nlr.h"
#include "py/compile.h"
#include "py/runtime.h"
#include "py/repl.h"
#include "py/gc.h"
#include "py/mphal.h"
#include "lib/mp-readline/readline.h"
#include "lib/utils/pyexec.h"
#include "mpthreadport.h"
#include "fdfile.h"

static const char* TAG = "python";

// MicroPython runs as a task under FreeRTOS
#define MP_TASK_PRIORITY        (ESP_TASK_PRIO_MIN + 1)
#define MP_TASK_STACK_SIZE      (6 * 1024)
#define MP_TASK_STACK_LEN       (MP_TASK_STACK_SIZE / sizeof(StackType_t))
#define MP_TASK_HEAP_SIZE       (32 * 1024)

STATIC StaticTask_t mp_task_tcb;
STATIC StackType_t mp_task_stack[MP_TASK_STACK_LEN] __attribute__((aligned (8)));
//STATIC uint8_t mp_task_heap[MP_TASK_HEAP_SIZE];

void mp_task(void *pvParameter) {
	uint8_t *mp_task_heap;
    volatile uint32_t sp = (uint32_t)get_sp();
    #if MICROPY_PY_THREAD
    mp_thread_init(&mp_task_stack[0], MP_TASK_STACK_LEN);
    #endif

    // TODO(supersat): Are these the right caps?
    // TODO(supersat): Move to new heap API
    // TODO(supersat): Move to a dynamic heap?! That would require a lot of work.
    mp_task_heap = heap_caps_malloc(MP_TASK_HEAP_SIZE, MALLOC_CAP_8BIT);
    if (!mp_task_heap) {
    	ESP_LOGW(TAG, "Cannot allocate %d bytes for the MicroPython heap", MP_TASK_HEAP_SIZE);
    	return;
    }
    ESP_LOGI(TAG, "MicroPython heap is at %p - %p", mp_task_heap, mp_task_heap + MP_TASK_HEAP_SIZE);
soft_reset:
    // initialise the stack pointer for the main thread
    mp_stack_set_top((void *)sp);
    mp_stack_set_limit(MP_TASK_STACK_SIZE - 1024);
    gc_init(mp_task_heap, mp_task_heap + MP_TASK_HEAP_SIZE);
    mp_init();
    mp_obj_list_init(mp_sys_path, 0);
    mp_obj_list_append(mp_sys_path, MP_OBJ_NEW_QSTR(MP_QSTR_));
    mp_obj_list_append(mp_sys_path, MP_OBJ_NEW_QSTR(MP_QSTR__slash_sdcard_slash_python));
    mp_obj_list_init(mp_sys_argv, 0);
    readline_init0();

    // run boot-up scripts
    pyexec_frozen_module("_boot.py");
    //pyexec_file("boot.py");
    //if (pyexec_mode_kind == PYEXEC_MODE_FRIENDLY_REPL) {
    //    pyexec_file("main.py");
    //}

    //ESP_LOGW(TAG, "Running telnetd -- VERY INSECURE");
    //pyexec_frozen_module("telnetd.py");

    ESP_LOGI(TAG, "Entering REPL loop");
    for (;;) {
        if (pyexec_mode_kind == PYEXEC_MODE_RAW_REPL) {
            if (pyexec_raw_repl() != 0) {
                break;
            }
        } else {
            if (pyexec_friendly_repl() != 0) {
                break;
            }
        }
    }

    #if MICROPY_PY_THREAD
    mp_thread_deinit();
    #endif

    mp_hal_stdout_tx_str("PYB: soft reboot\r\n");

    mp_deinit();
    fflush(stdout);
    goto soft_reset;
}

extern mp_obj_fdfile_t mp_sys_stdin_obj;
extern mp_obj_fdfile_t mp_sys_stdout_obj;
extern mp_obj_fdfile_t mp_sys_stderr_obj;

void python_start(void) {
	uart_driver_install(UART_NUM_0, 256, 0, 0, NULL, 0);

	mp_sys_stdin_obj.fd = stdin->_file;
	mp_sys_stdout_obj.fd = stdout->_file;
	mp_sys_stderr_obj.fd = stderr->_file;

    xTaskCreateStaticPinnedToCore(mp_task, "mp_task", MP_TASK_STACK_LEN, NULL, MP_TASK_PRIORITY,
                                  &mp_task_stack[0], &mp_task_tcb, 0);
}

uint mp_import_stat(const char *path) {
    struct stat st;
    if (stat(path, &st) == 0) {
        if (S_ISDIR(st.st_mode)) {
            return MP_IMPORT_STAT_DIR;
        } else if (S_ISREG(st.st_mode)) {
            return MP_IMPORT_STAT_FILE;
        }
    }
    return MP_IMPORT_STAT_NO_EXIST;
}

void nlr_jump_fail(void *val) {
    printf("NLR jump failed, val=%p\n", val);
    assert(0);
    esp_restart();
}

// modussl_mbedtls uses this function but it's not enabled in ESP IDF
void mbedtls_debug_set_threshold(int threshold) {
    (void)threshold;
}
