cryptovillage/badge2017/firmware/esp32/main/display.h

/*
 * display.h
 *
 *  Created on: Apr 4, 2017
 *      Author: supersat
 */

#ifndef MAIN_DISPLAY_H_
#define MAIN_DISPLAY_H_

extern void display_test();
extern void display_on();
extern void display_off();
extern void display_enable();
extern void display_disable();
extern void display_init();
extern void display_show_logo();

#endif /* MAIN_DISPLAY_H_ */
