cryptovillage/badge2017/firmware/esp32/main/sdcard.h

/*
 * sdcard.h
 *
 *  Created on: Jul 4, 2017
 *      Author: supersat
 */

#ifndef MAIN_SDCARD_H_
#define MAIN_SDCARD_H_

extern void sdcard_init();
extern void sdcard_test();

#endif /* MAIN_SDCARD_H_ */
