cryptovillage/badge2017/firmware/esp32/main/shared.h

/*
 * shared.h
 *
 *  Created on: Apr 10, 2017
 *      Author: supersat
 */

#ifndef MAIN_SHARED_H_
#define MAIN_SHARED_H_

typedef char INT8;
typedef short INT16;
typedef int INT32;
typedef unsigned char uint8;
typedef unsigned char UINT8;
typedef unsigned short UINT16;
typedef unsigned int UINT32;

//#define INLINE inline
#define INLINE

#include <string.h>
#include <math.h>
#include "ym2612.h"

#endif /* MAIN_SHARED_H_ */
